erhickey/t_rexth/artwork/original_black.png

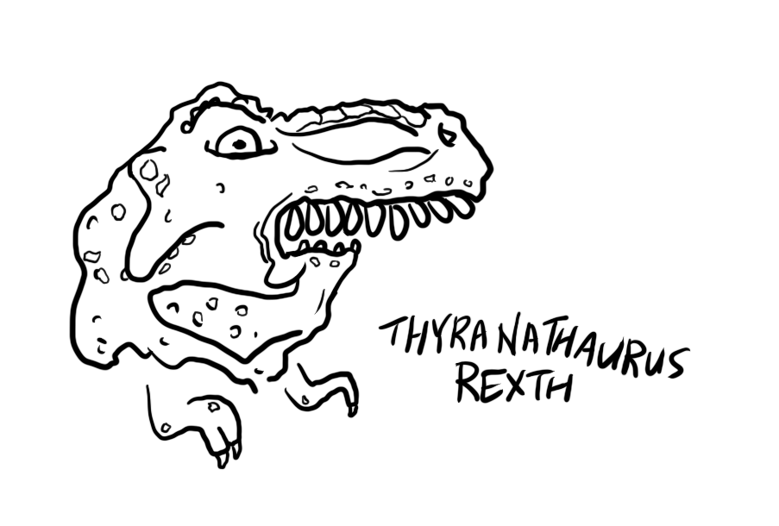
artwork/original_black.png
