erhickey/t_rexth/artwork/original_white.png

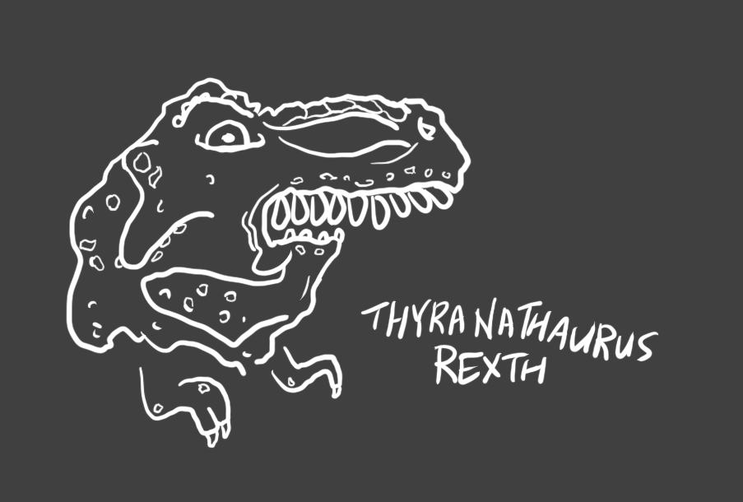
artwork/original_white.png
