erhickey/t_rexth/artwork/text_cropped.png

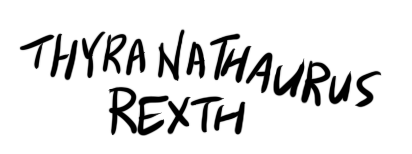
artwork/text_cropped.png
